Tonikiller10000/KeystrokeInjectionTool/KeystrokeInjectionTool_V2.0/KeystrokeInjTool_Pictures/20230904_132029.jpg

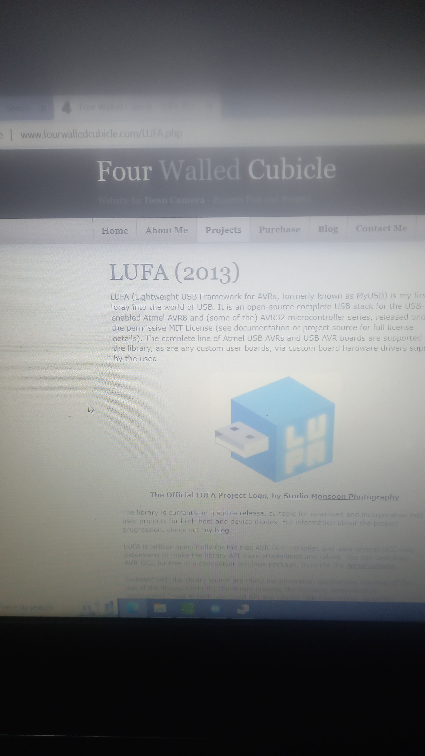
KeystrokeInjectionTool_V2.0/KeystrokeInjTool_Pictures/20230904_132029.jpg
