Tonikiller10000/KeystrokeInjectionTool/KeystrokeInjectionTool_V2.0/KeystrokeInjTool_Pictures/p1.jpg

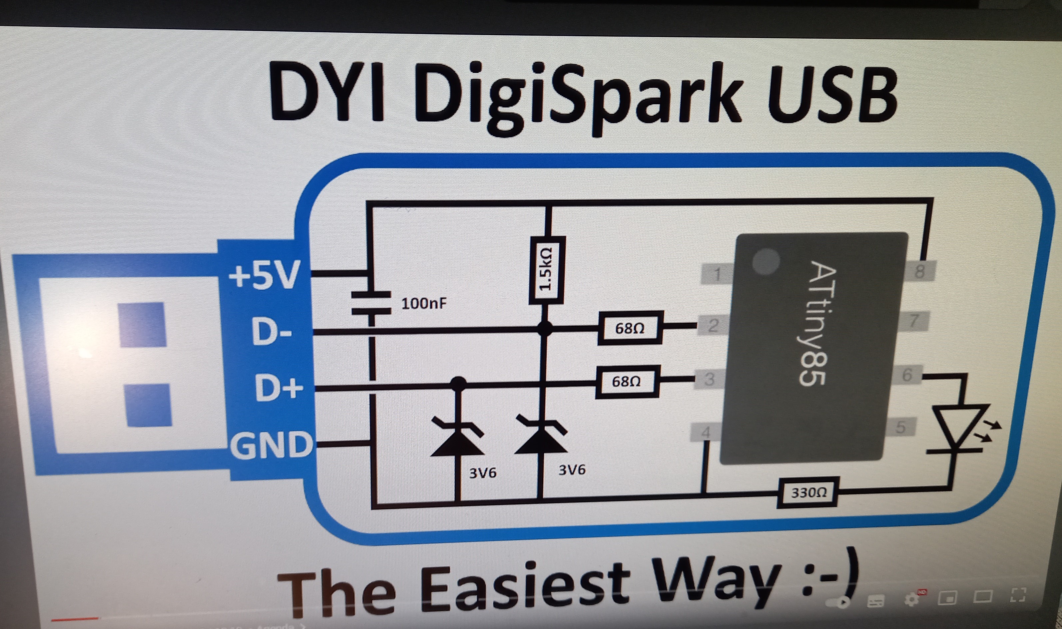
KeystrokeInjectionTool_V2.0/KeystrokeInjTool_Pictures/p1.jpg
