Tonikiller10000/KeystrokeInjectionTool/KeystrokeInjectionTool_V2.0/KeystrokeInjTool_Pictures/p2.png

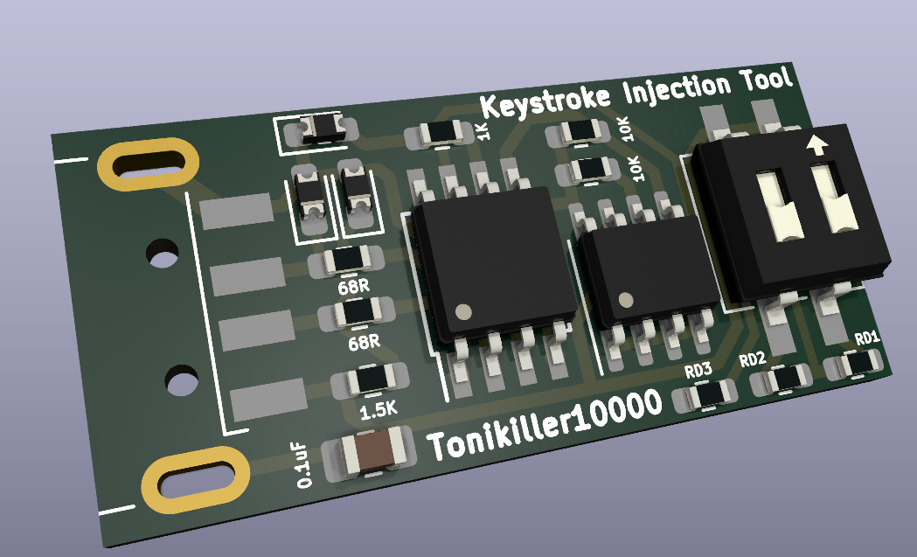
KeystrokeInjectionTool_V2.0/KeystrokeInjTool_Pictures/p2.png
