Tonikiller10000/KeystrokeInjectionTool/KeystrokeInjectionTool_V2.0/KeystrokeInjTool_Pictures/Screenshot 2024-01-30 201155.png

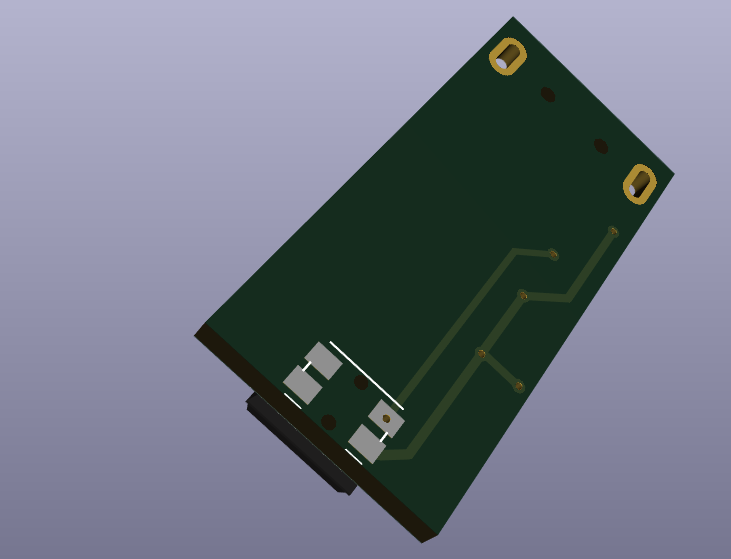
KeystrokeInjectionTool_V2.0/KeystrokeInjTool_Pictures/Screenshot 2024-01-30 201155.png
