Tonikiller10000/KeystrokeInjectionTool/KeystrokeInjectionTool_V2.0/KeystrokeInjTool_Pictures/Screenshot_20230306-094918_Chrome.jpg

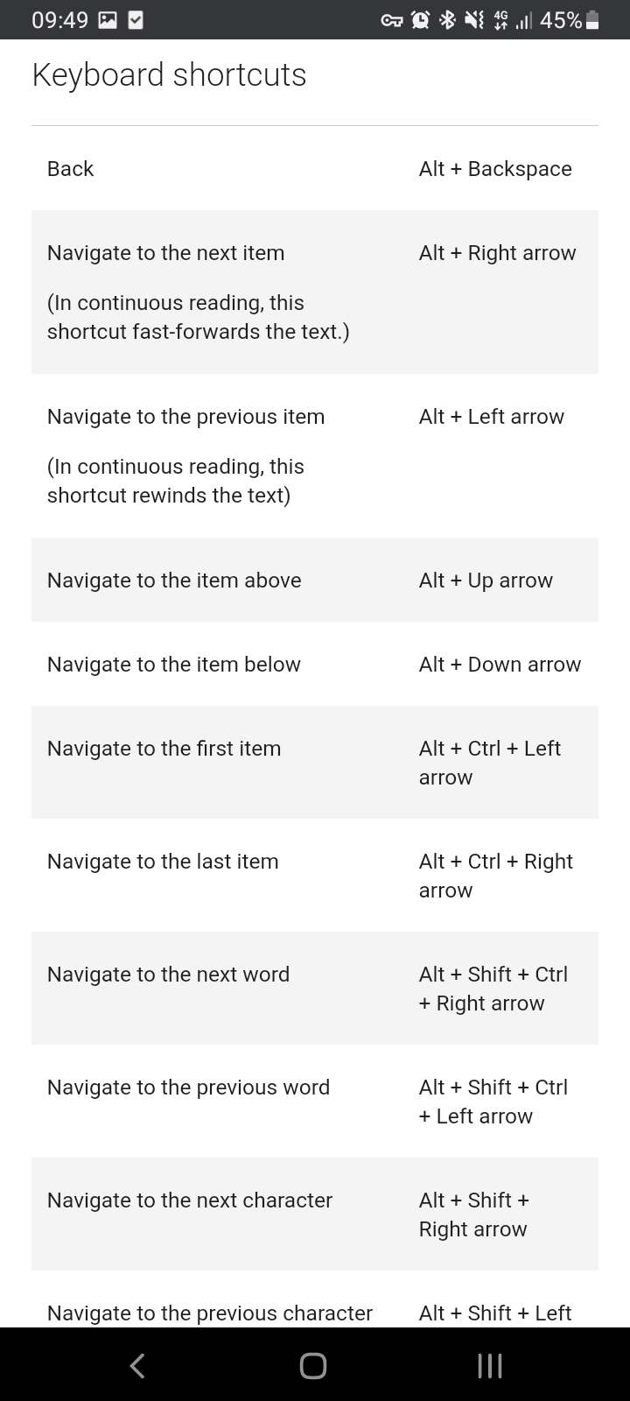
KeystrokeInjectionTool_V2.0/KeystrokeInjTool_Pictures/Screenshot_20230306-094918_Chrome.jpg
