Tonikiller10000/KeystrokeInjectionTool/KeystrokeInjectionTool_V2.0/KeystrokeInjTool_Pictures/Screenshot_20230331-075846_Chrome.jpg

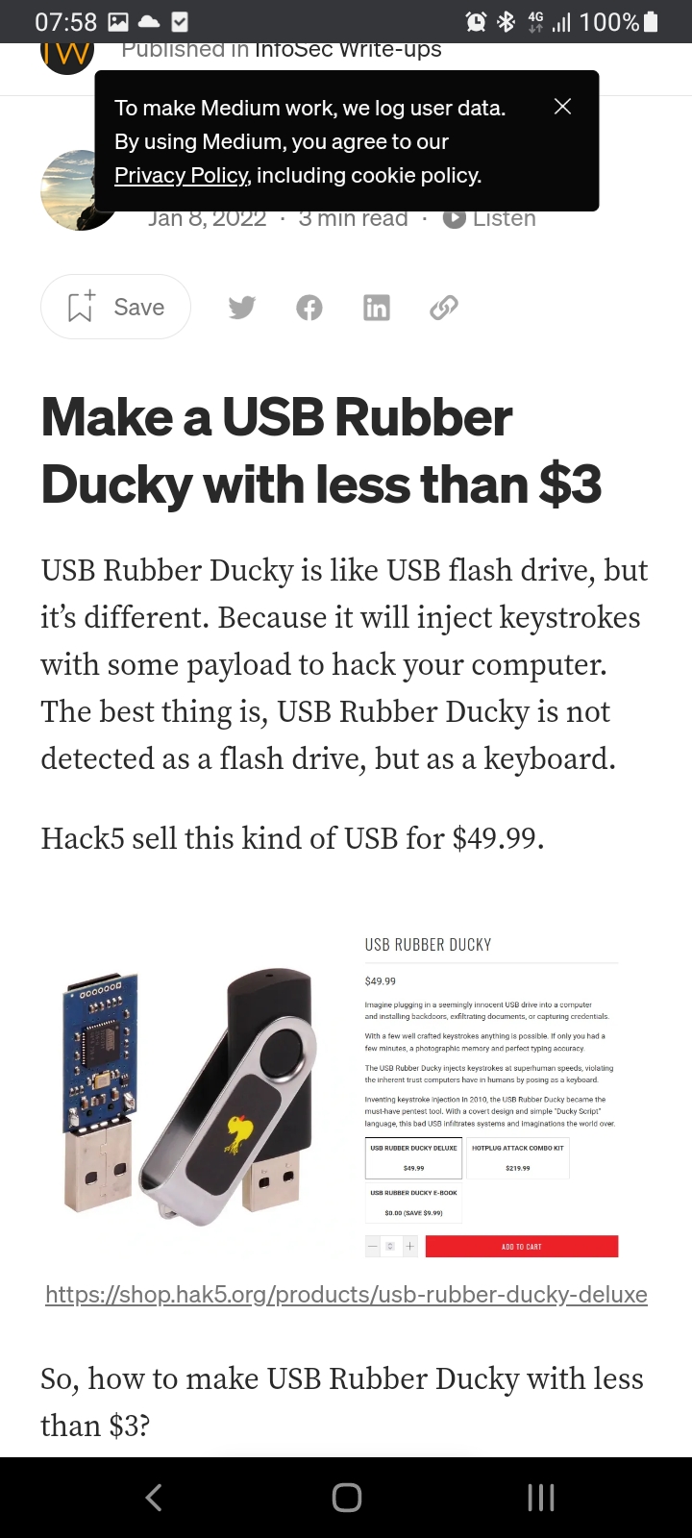
KeystrokeInjectionTool_V2.0/KeystrokeInjTool_Pictures/Screenshot_20230331-075846_Chrome.jpg
